alesti/iso9001/stl-Files/Valve/Valve_cover.stl

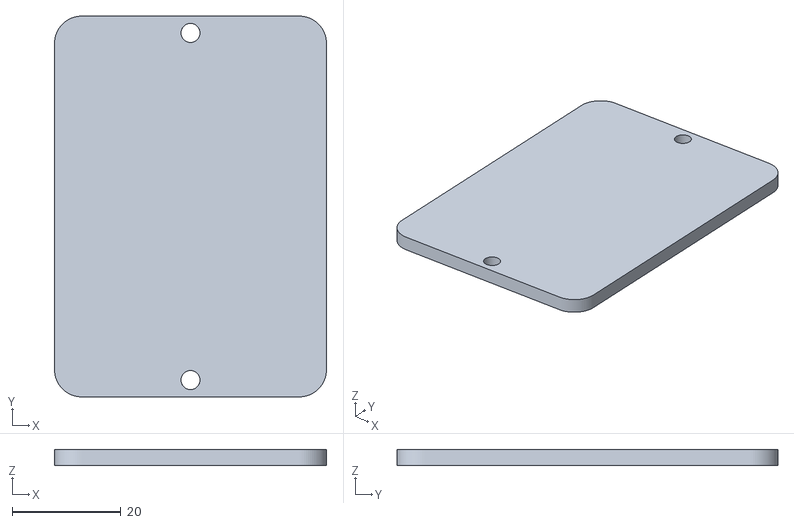
[picture p15: CAD file, 2019-07-24]
stl-Files/Valve/Valve_cover.stl
50.0 x 70.0 x 3.00
