alesti/iso9001/stl-Files/Arm/Arm_trigger.stl

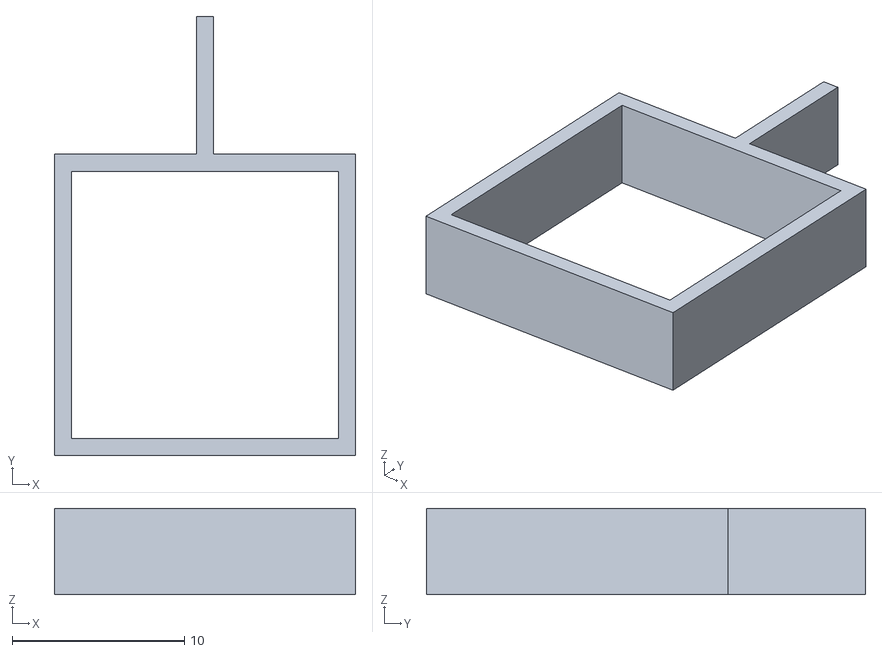
[picture p16: CAD file, 2019-07-24]
stl-Files/Arm/Arm_trigger.stl
17.5 x 25.5 x 5.00
