alesti/iso9001/stl-Files/Bell/Bell_servo-bracket.stl

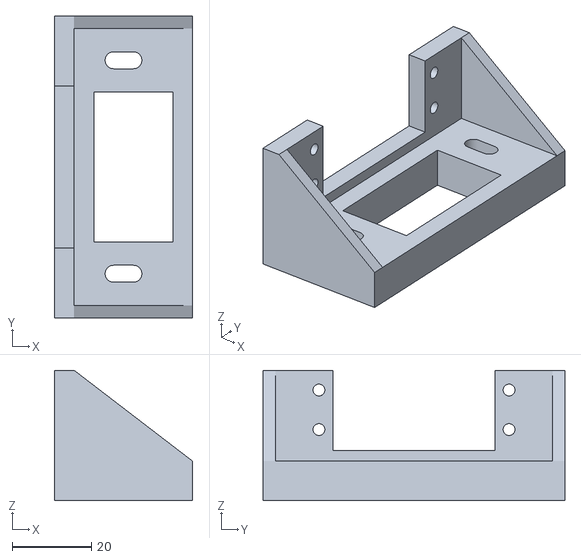
[picture p17: CAD file, 2019-07-24]
stl-Files/Bell/Bell_servo-bracket.stl
35.0 x 76.4 x 33.0
