alesti/iso9001/stl-Files/Display/Display_base.stl

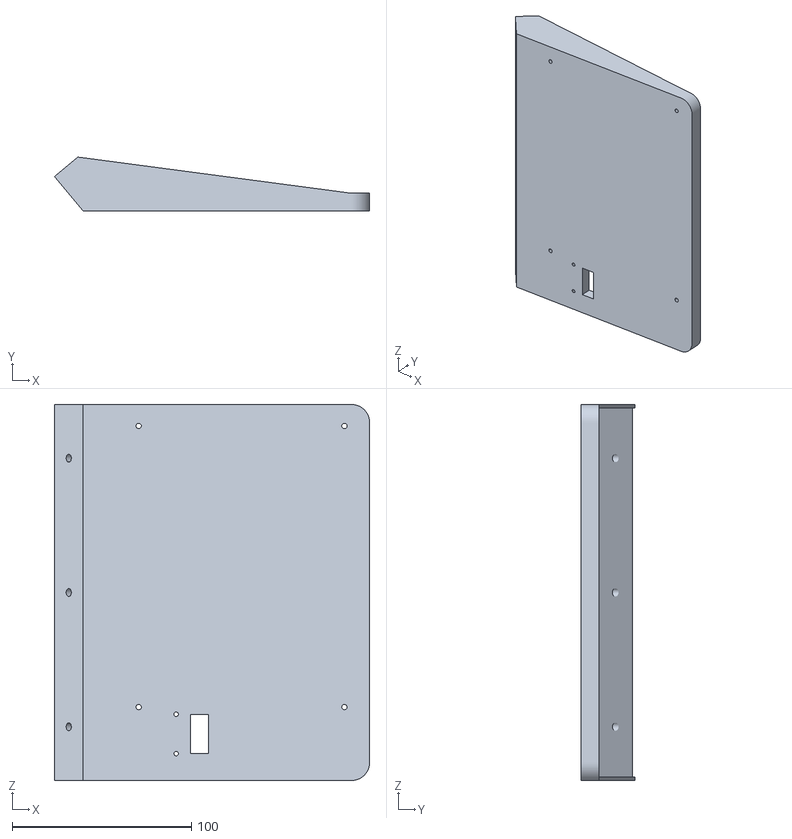
[picture p18: CAD file, 2019-07-24]
stl-Files/Display/Display_base.stl
176.0 x 30.1 x 210.0
