alesti/iso9001/stl-Files/Misc/Flush-funnel_B.stl

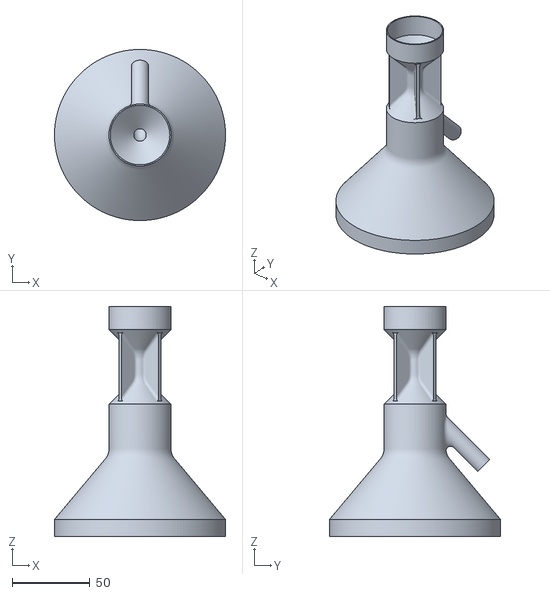
[picture p19: CAD file, 2019-07-24]
stl-Files/Misc/Flush-funnel_B.stl
110.4 x 110.4 x 148.4
