alesti/iso9001/stl-Files/Scale/Scale_cover.stl

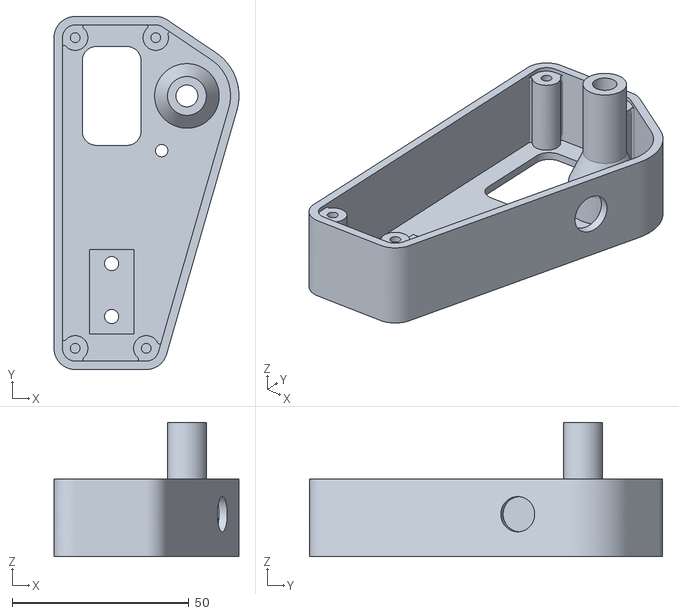
[picture p20: CAD file, 2019-07-24]
stl-Files/Scale/Scale_cover.stl
52.4 x 100.0 x 38.0
