alesti/iso9001/stl-Files/Valve/Valve_tongue.stl

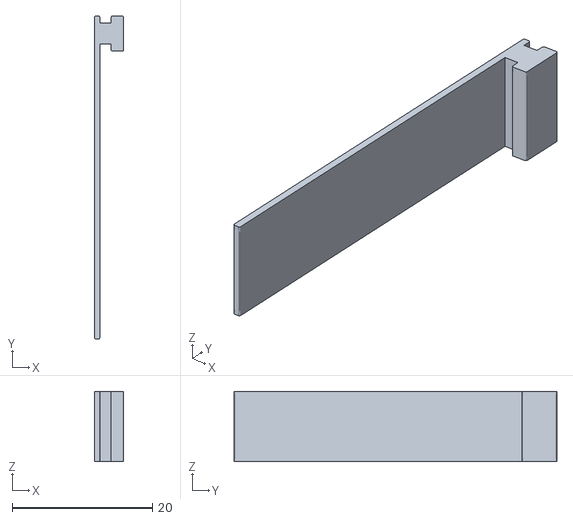
[picture p21: CAD file, 2019-07-24]
stl-Files/Valve/Valve_tongue.stl
4.20 x 46.0 x 10.0
