alesti/iso9001/stl-Files/Arm/Arm_pinion.stl

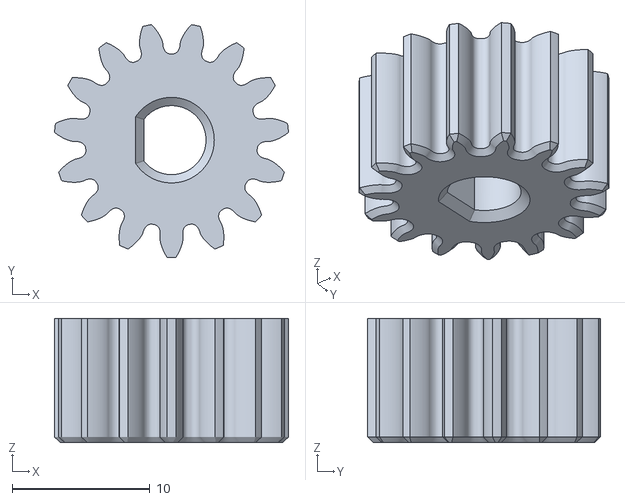
[picture p22: CAD file, 2019-07-24]
stl-Files/Arm/Arm_pinion.stl
17.0 x 16.9 x 9.00
