alesti/iso9001/stl-Files/Misc/Rubberplug_core_insert.stl

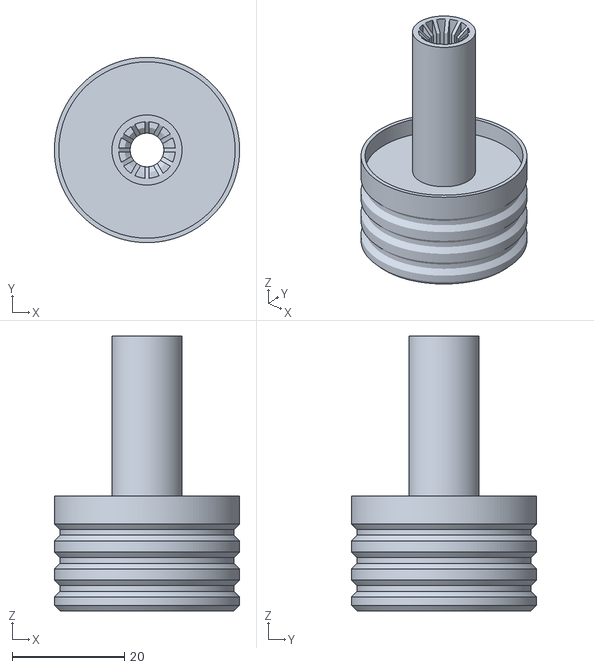
[picture p23: CAD file, 2019-07-24]
stl-Files/Misc/Rubberplug_core_insert.stl
33.0 x 33.0 x 49.0
