alesti/iso9001/stl-Files/Scale/Scale_spacer.stl

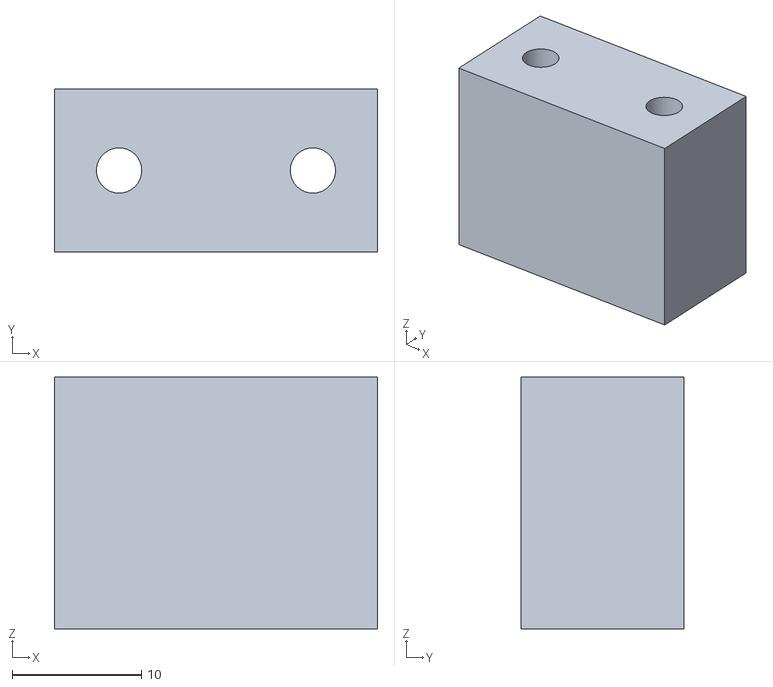
[picture p24: CAD file, 2019-07-24]
stl-Files/Scale/Scale_spacer.stl
25.0 x 12.6 x 19.5
