alesti/iso9001/stl-Files/Valve/Valve_cam_EZ_Rev.0.stl

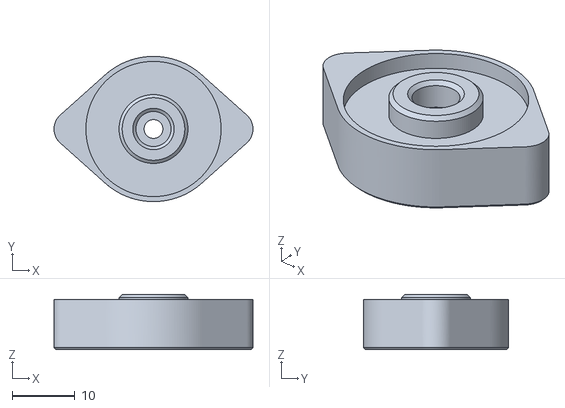
[picture p25: CAD file, 2019-07-24]
stl-Files/Valve/Valve_cam_EZ_Rev.0.stl
31.8 x 23.2 x 8.80
