alesti/iso9001/stl-Files/Arm/Arm_drip_pan.stl

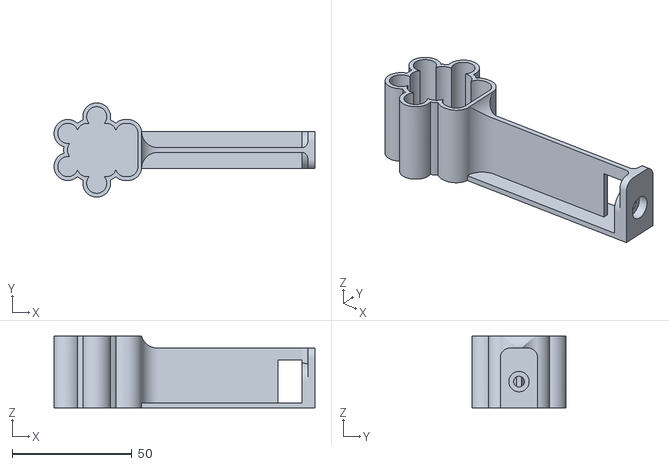
[picture p26: CAD file, 2019-07-24]
stl-Files/Arm/Arm_drip_pan.stl
108.8 x 39.3 x 30.0
