alesti/iso9001/stl-Files/Misc/Rubberplug_core.stl

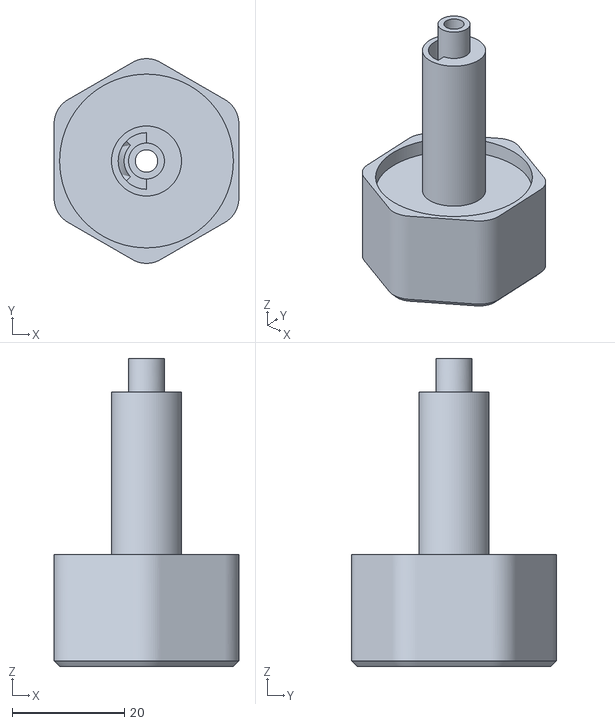
[picture p27: CAD file, 2019-07-24]
stl-Files/Misc/Rubberplug_core.stl
33.0 x 36.6 x 55.0
