alesti/iso9001/stl-Files/Scale/Scale_lid.stl

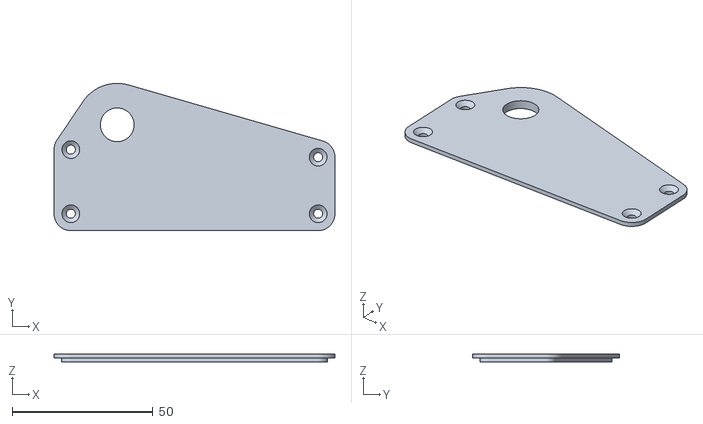
[picture p28: CAD file, 2019-07-24]
stl-Files/Scale/Scale_lid.stl
100.0 x 52.4 x 3.00
