alesti/iso9001/stl-Files/Valve/Valve_cam.stl

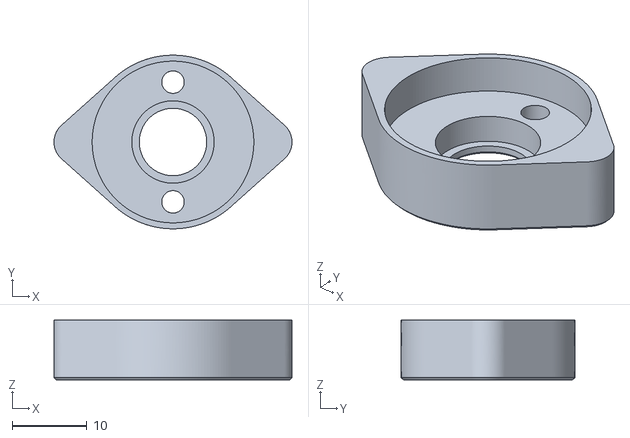
[picture p29: CAD file, 2019-07-24]
stl-Files/Valve/Valve_cam.stl
31.8 x 23.2 x 8.00
