alesti/iso9001/stl-Files/Arm/Arm_mount.stl

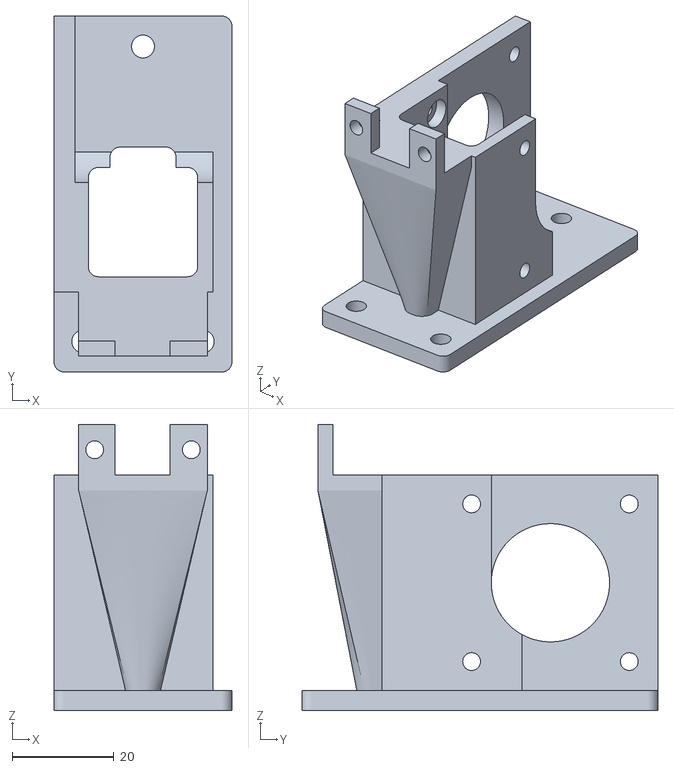
[picture p30: CAD file, 2019-07-24]
stl-Files/Arm/Arm_mount.stl
35.0 x 70.0 x 56.3
