alesti/iso9001/stl-Files/Scale/Scale_pan.stl

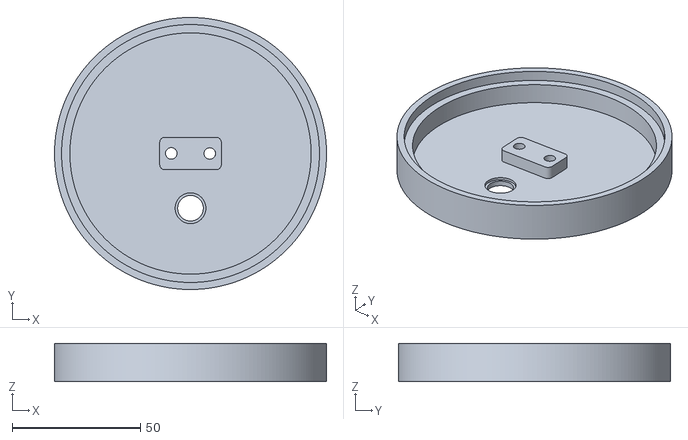
[picture p31: CAD file, 2019-07-24]
stl-Files/Scale/Scale_pan.stl
106.0 x 106.0 x 15.0
