alesti/iso9001/stl-Files/Arm/Arm_rack.stl

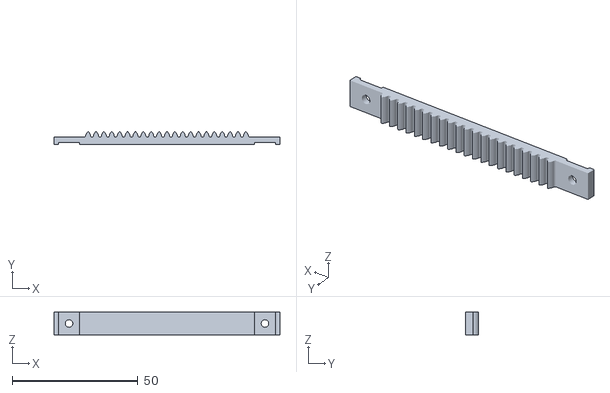
[picture p32: CAD file, 2019-07-24]
stl-Files/Arm/Arm_rack.stl
90.0 x 5.00 x 9.00
